kushagr-m/senior-robotics/designs/stl/WheelMount.stl

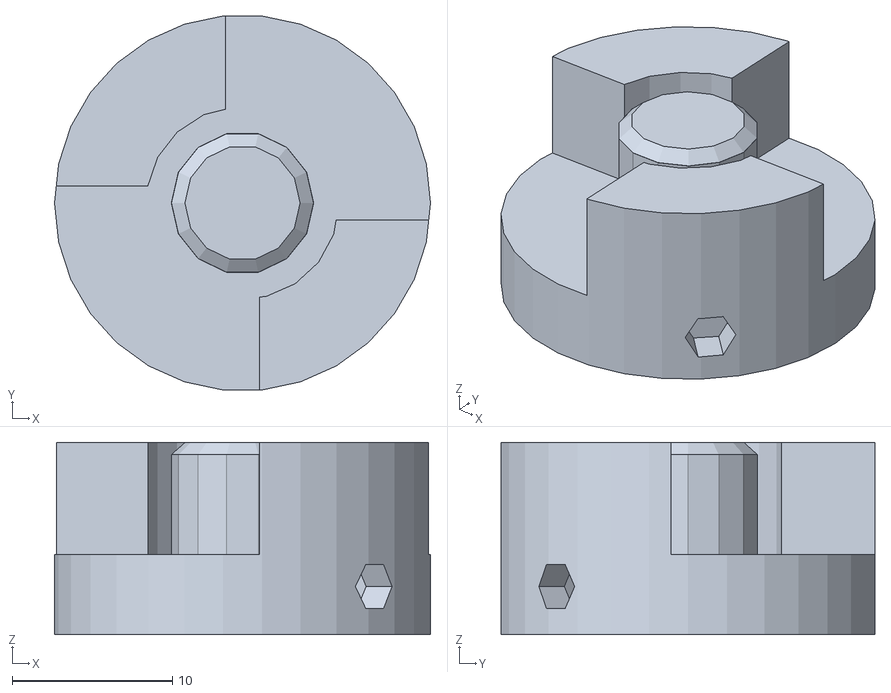
[picture p16: CAD file, 2018-09-28]
designs/stl/WheelMount.stl
23.5 x 23.4 x 12.0
