kushagr-m/senior-robotics/src/hardware/phobot/serial_read.py

import serial
ser = serial.Serial('/dev/ttyACM0',115200) # change to ACM1 if that is the USB port

while True:
    readSerial=ser.readline() # reads from serial until EOL character received - i.e. \n
    
    if ':' in readSerial:
        dataTOF = readSerial
    else:
        dataCompass = readSerial
