kushagr-m/senior-robotics/src/threaded/vision.py

from imutils.video import VideoStream
import imutils
import time
from threading import Thread
import numpy as np
import math
import cv2 as cv
import collections

class VisionProcess:
	def __init__(self):

		print('Initialising Vision Process...')
		self.frameDimensions = (320,240) # set frame dimensions

		# initialise variables
		self.ballArea = 0
		self.stopped = False
		self.vs = None
		self.rotateFrame = False
		self.maxVal = None

		self.frameCount = 0
		self.fpsTime = time.perf_counter()
		self.currentFPS = 0
		self.hsvatBallCenter = (0,0,0)
		
		self.noBallDetected = True
		self.currentBallCenter = None
		self.relativeBallCenter = None

		self.outlineCenter, self.outlineRadius = None,None
		self.rgb, self.ballGrayscale, self.ballMask, self.hsvMask = None, None, None, None

		self.ballCenterQueue = collections.deque(maxlen=200)

		print('VisProc: Getting camera.')

		for i in [2,1,0]:
			print('VisProc: Trying webcam ',i,'...',sep='')
			vs = VideoStream(src=i).start()
			time.sleep(0.1) # warmup time
			try:
				vs.read().any()
				self.vs = vs
				print('VisProc: Webcam',i,'successful.')
				break
			except: pass
		
		if self.vs is None:
			print('VisProc: all webcams unsuccessful.')
			try:
				self.vs = VideoStream(usePiCamera=True).start()
				self.rotateFrame = True
				print('VisProc: Trying PiCamera.')
				time.sleep(2.0)
				vs.read().any()
				print('VisProc: PiCamera successful.')
			except Exception as e:
				print('VisProc: PiCamera Failed.')
				print(e)
				#raise Exception('No camera found.')

	def start(self):
		t = Thread(target=self.Process,args=(),name='VisionProcess')
		t.daemon = True
		t.start()
		return self

	def GetFrame(self):
		rgb = imutils.resize(self.vs.read(),self.frameDimensions[0])
		#rgb = cv.GaussianBlur(rgb,(11,11),0)
		if self.rotateFrame:
			rgb = imutils.rotate(rgb,180)
		hsv = cv.cvtColor(rgb, cv.COLOR_BGR2HSV)
		return rgb, hsv

	def OutputFrame(self):
		return self.rgb, self.ballGrayscale, self.ballMask, self.hsvMask

	def Process(self):
		while not self.stopped:

			self.rgb, self.hsv = self.GetFrame()
			rgbB,rgbG,rgbR = cv.split(self.rgb)
			hsvH,hsvS,hsvV = cv.split(self.hsv)
			self.ballGrayscale = cv.subtract(rgbR,rgbB)
			
			self.hsvMask = cv.bitwise_and(cv.inRange(hsvS,100,255),cv.bitwise_or(cv.inRange(hsvH,0,4),cv.inRange(hsvH,175,180)))
			maxVal = cv.minMaxLoc(self.ballGrayscale, self.hsvMask)[1]

			ballCenterForCalcs = None

			if maxVal >= 70:

				noBallDetected = False

				self.ballMask = cv.erode(cv.bitwise_and(cv.inRange(self.ballGrayscale,(maxVal-45),255),self.hsvMask),cv.getStructuringElement(cv.MORPH_RECT,(5,5)))

				#self.ballMask = cv.dilate(self.ballMask,cv.getStructuringElement(cv.MORPH_ELLIPSE,(17,17)))
				moments = cv.moments(self.ballMask)
				self.ballArea = moments['m00']
				if moments:
					if moments["m00"]<=0: ballCenterForCalcs = int(moments["m10"]),int(moments["m01"])
					else: ballCenterForCalcs = int(moments["m10"] / moments["m00"]), int(moments["m01"] / moments["m00"])
					
					self.ballMask, ballOutline, hierarchy = cv.findContours(self.ballMask,cv.RETR_EXTERNAL,cv.CHAIN_APPROX_SIMPLE) # get the outline of self.ballMask
					# if ballOutline is not None:
					# 	try:
					# 		self.outlineCenter,self.outlineRadius = cv.minEnclosingCircle(ballOutline[0])
					# 		strX,strY,strW,strH = cv.boundingRect(ballOutline[0])
					# 		outlineRect = cv.minAreaRect(ballOutline[0])
					# 		outlineBox = np.int0(cv.boxPoints(outlineRect))
					# 		if ((outlineRadius/strH)>1) or (strW/strH)>=1.5 or (strH<(outlineRadius*1.5)): 
					# 			noBallDetected = True
					# 	except: 
					# 		#print('Could not get outlineCenter and radius')
					# 		pass

					self.hsvatBallCenter = self.hsv[ballCenterForCalcs[1]][ballCenterForCalcs[0]]
					if self.hsvatBallCenter[0] > 5 and self.hsvatBallCenter[0] < 175: 
						noBallDetected = True

					if ballCenterForCalcs == (0,0): noBallDetected = True

				else: noBallDetected = True
			else: noBallDetected = True

			self.currentBallCenter = ballCenterForCalcs

			if self.currentBallCenter is not None:
				self.relativeBallCenter = (int(self.currentBallCenter[0]-(self.frameDimensions[0]/2)), int(self.currentBallCenter[1]-(self.frameDimensions[1]/2)))
				self.ballCenterQueue.append(self.relativeBallCenter)

			self.frameCount = self.frameCount + 1
			if self.frameCount % 5 == 0:
				# Recalculate fps every 30 frames
				currentTime = time.perf_counter()
				self.currentFPS = math.floor(5 / (currentTime - self.fpsTime))
				self.fpsTime = currentTime

			self.noBallDetected = noBallDetected
			if maxVal is not None: self.maxVal = maxVal
	
		print('VisProc: Stopped.')
		self.vs.stop()
		return

	def read(self):
		return (not self.noBallDetected), self.relativeBallCenter, self.ballCenterQueue, self.ballArea

	def readDebug(self):
		return self.hsvatBallCenter, self.currentFPS, self.maxVal

	def minEnclosing(self):
		if self.outlineCenter and self.outlineRadius: return self.outlineCenter,self.outlineRadius
		else: return None,None

	def stop(self):
		self.stopped = True
